Harwasch/MakeHardware/docs/00-stack.md

# The stack, and why

Every choice below was run in a real Claude Code cloud VM (Ubuntu 24.04,
4 vCPU / 16 GB / 30 GB) before it was written down. Timings are measured, not
estimated.

## What we run

| Layer | Tool | Why this one |
|---|---|---|
| Planning | **plan.yaml** + `plan-render` | Session-sized chunks with explicit dependencies, scheduled by longest path, rendered as a dependency Gantt into the README. |
| Requirements | **StrictDoc** 0.28.3 | Plain-text `.sdoc` in git, typed grammar, parent/child relations, refuses to build a tree with a dangling parent or duplicate UID. Exports HTML, JSON and ReqIF. |
| Schematic / PCB | **KiCad 10** + **[KiStack](https://github.com/American-Embedded/KiStack)** (MIT) | Ten skills, not a server: human-written house practice for schematic work, layout, BOM, exports, panelisation and Gerber review, plus a reference page for every `kicad-cli` verb. |
| PCB checks & output | **kicad-cli** | ERC, DRC, netlist, gerbers, STEP. Headless, scriptable, no GUI needed. |
| Circuit simulation | **ngspice 42** via **ltspice-mcp** 0.5.0 | Headless, no Wine, first-class backend in the MCP server. Returns parsed measurements, not plots. |
| Circuit simulation (opt-in) | **LTspice** under Wine | Only for vendor-encrypted ADI models and `.asc` editing. Off by default. |
| 3D CAD | **build123d** 0.11.1 + **build123d-mcp** | Parametric Python CAD on OCCT. Models are code, so they diff, review and re-render on a changed number. |
| Meshing / FEA | **gmsh** 4.12.1 + **CalculiX** 2.21 | Both in the Ubuntu archive, both headless. Thermal and structural. |
| Magnetics | **FastHenry** 3.0.1 + **Elmer** 26.2 (`elmerfem-csc`, elmer-csc PPA) + **GetDP** 3.2.0 | SPICE cannot tell you an inductance. FastHenry is PEEC — no air mesh, seconds for L, M, k and R_ac of air-core conductors; Elmer does the cases with ferrite in them. See the `hw-magnetics` skill for which answers what. |
| Design gates | **`sch-lint`**, **`pcb-lint`**, **`cad-export`** | In-tree, read-only, no KiCad and no MCP server needed. They measure the things ERC and DRC have no opinion about: whether a human can read the drawing, whether the net classes are physically routable, whether the CAD file is an assembly or a lump. |
| Figures | **`hw-chart`** | Eight engineering plots as themed SVG, 2-9 kB each, generated from the file that owns the numbers. |
| Design loops | **`hw-iterate`** | A ledger of every verify-and-refine pass — variables, measured metrics, the run file each number came from — and the evolution chart drawn from it. What turns "it meets the target" into something a reviewer can check. |
| Environment repair | **`hw-repair`** | Installs, at run time, what the environment build failed to — base packages, any one of phase_python's install groups, Elmer, the KiCad skill pack. A degraded snapshot is otherwise a dead session until somebody rebuilds the environment. `env/bootstrap.sh` is the from-nothing case. |
| Design review | **kicad-happy** (MIT) | Read-only analysers nothing else here has: EMC pre-compliance, thermal, voltage derating, datasheet cross-reference, distributor search. Pure Python, needs no KiCad install. |
| Vision renders | **matplotlib** + build123d tessellation | Shaded views and isometric line art from real geometry. |
| Vision styling | **Hugging Face Spaces** (FLUX Kontext, Qwen) | Restyles a geometry render without inventing new proportions. No API key needed. |

## The decisions worth arguing about

### ngspice is the default simulator, not LTspice

The original draft made LTspice authoritative. Three things argue against it:

1. `ltspice.analog.com` is **not** in the Trusted network allowlist, so the
   MSI download fails and takes the setup script down with it.
2. Wine plus the MSI is roughly 2 GB and several minutes of the ~5 minute
   environment-build budget.
3. `ltspice-mcp` treats ngspice as a first-class backend — "simulate, parse,
   diagnose, analyze… open-source path with no LTspice install".

ngspice runs headless, starts instantly and needs no allowlist change. An RC
low-pass measured `fc = 997.7 Hz` against 1 kHz theoretical on the first run.

LTspice is still worth having when you need vendor-encrypted ADI models or
`.asc` schematic editing — set `MH_ENABLE_LTSPICE=1` and add `*.analog.com`
to the allowlist. It is a supplement, not the foundation.

### KiCad 10 must come from the PPA, and that needs an allowlist entry

Ubuntu 24.04 universe carries **KiCad 7.0.11**, which has no IPC API and no
`kicad-cli` worth the name, so neither substrate works against it.
KiCad 10 is published for noble on the KiCad PPA.

The trap: PPA content is served from `ppa.launchpadcontent.net`, and the
Trusted allowlist names only `launchpad.net` and the **retired**
`ppa.launchpad.net` (which now fails to connect at all). So without a Custom
allowlist entry, `apt-get update` prints a warning, **still exits 0**, and
`apt-get install kicad` quietly installs KiCad 7 from universe. The failure is
silent and lands three steps later as "the IPC socket does not answer".

`env/setup.sh` pins the PPA with an apt preference and then explicitly asserts
the installed major version, so this fails loudly instead.

Worth knowing that the loud failure was itself wrong for a while. The check
was `apt-cache policy kicad | grep -q "kicad-10.0-releases"`, and under
`set -o pipefail` a *matching* grep exits first, `apt-cache` takes SIGPIPE, and
the pipeline reports 141. So the phase announced "PPA unreachable" on builds
where the PPA was reachable, the index fetched and the candidate correctly
pinned at 10.0.5 — and KiCad never got installed. The check now captures the
output and matches it with `case`. See `docs/01-environment.md`.

### The KiCad substrate: skills, not a tool surface

This slot has held three things. Konnect (an MCP server: one Rust binary, 214
tools over KiCad 10's IPC API) through 0.6.0; [ki-stack](https://github.com/Milind220/ki-stack)
through 0.7.0; [KiStack](https://github.com/American-Embedded/KiStack) now.
Both replacements are skills rather than servers, and that part of the argument
has held up twice:

* **A tool surface costs context whether or not it is used.** Konnect answered
  this by loading 2 of its 20 toolsets at startup and making the agent call
  `load_toolset` for the rest — which is a real cost paid in round trips and in
  failures that read as "the tool is missing". A skill costs nothing until it
  loads.
* **The failure mode is different in kind.** A missing tool is a wall. A skill
  that names its fallback is a route. That is the same reasoning `hw-optimize`
  applies to everything else in the toolbox.

`kicad-cli` has no `add`, `place`, `route` or `connect` verb on KiCad 10 and
never has, so *something* has to author. The question is only whether that is
pre-sliced verbs or the agent driving `kipy` and the design files with
judgement about which.

**Why KiStack over ki-stack.** They are different books. ki-stack is a manual
for the *substrates* — how to route between IPC, CLI and structured file edits.
KiStack is house practice from a working shop: what a good schematic looks
like, how to place before routing, when a pin swap is worth it, how to read a
Gerber. This toolbox already had the substrate question answered in
`hw-schematic` and `hw-pcb-layout`; what it did not have was the craft.

The cost is that KiStack overlaps those two skills and disagrees with them in
places — chiefly the sheet strategy, where KiStack prefers one big sheet and
this toolbox derives a sheet plan from the agreed block diagram. The rule is
**the gate wins**: `sch-lint`, `pcb-lint` and `review-gate` are what actually
fail a stage, and advice that passes review while failing a gate is not
shippable. `hw-schematic/references/kicad-channels.md` carries the table.

Neither swap kept Konnect's design-review audits or its manufacturing pipeline.
`sch-lint`, `pcb-lint`, `hw-verification` and kicad-happy cover most of that
ground, which is why the loss is acceptable — but it is a loss, not a wash.

The pack is a **pinned clone**, not a vendored copy: these are instructions an
agent follows, so an unpinned checkout means the guidance under a project can
change between sessions with nothing in the repo recording it. MIT, so
vendoring would be permitted — pinning is better because
`git -C /opt/kistack` still knows what revision it is on.

### Image generation comes from the Hugging Face connector

The vision stage wants real imagery for styling, and there is no image model in
the environment itself. The connector already attached to this account exposes
FLUX, Qwen and — the important one — `FLUX.1-Kontext-Dev`, which *edits* an
input image. Seeding it with a build123d render keeps the proportions honest
while restyling material and finish, which a pure text-to-image model cannot
do.

It needs no API key and no allowlist entry. The one catch is a `gradio=none`
header on the connector that disables `invoke`; see
`docs/01-environment.md`. A paid direct API remains the upgrade path when
shared-GPU latency stops being acceptable.

### Live IPC needs a running KiCad; nothing else does

`kicad-python` talks to an application, not a file. So board work through IPC
needs a KiCad up (`hw-kicad-up`, which starts Xvfb and the GUI), while render,
export, ERC, DRC and structured file edits all run headless.

This matters because the environment snapshot preserves **files, not
processes** — a KiCad started during setup is gone by the time a session runs.
Schematic work in particular is usually better off on the offline structured
route than on IPC, so the default posture is headless and the GUI is an
escalation.

### KiStack and kicad-happy are complementary, not competing

Both provide KiCad skills and their triggers overlap. They do different jobs:
KiStack *changes* designs, through the IPC bindings or the files themselves.
kicad-happy *reads* them — pure Python analysers producing structured reports,
plus distributor search and datasheet extraction.

So the rule is: writes go through KiStack, reads go through kicad-happy, and
the decision about which part to actually buy stays in `hw-sourcing` where the
house standards live. The full precedence table ships in the project
`CLAUDE.md`.

### The linters parse KiCad files themselves, and that is not a contradiction

The house rule — nothing writes a `.kicad_*` file except KiCad, its IPC
bindings, or a structured parser that round-trips it — stands and is not
weakened. It is about **writes**: a hand-rolled text edit corrupts those files.
Reading one is a different act, and a gate has to run headless in a container
with no KiCad and no third-party packages, so
`scripts/kicad_sexpr.py` is a ~250-line reader that does exactly that and
nothing else. Verified against both dialects present in this image: the KiCad 7
schematic fixture and KiCad 10's own shipped boards.

The board fixture the PCB linter is developed against is **generated by
`pcbnew`**, which is the escape hatch `pcb-layout.md` §0 already endorses.

### FreeCAD is not installed, and the CAD assemblies still carry their joints

STEP does not carry mates. AP242 edition 2 defines kinematics, OCCT does not
write them, and FreeCAD does not read them — so there is no portable format
that moves an editable constraint between CAD tools today.

Ubuntu 24.04 ships FreeCAD 0.21, which has no Assembly workbench at all; 1.0 is
the first version with one, and an AppImage would need an allowlist entry and
would not fit the five-minute build budget. So `cad-export` writes a **macro**
the human runs in their own FreeCAD 1.0, and runs it here only if a suitable
`freecadcmd` happens to be on `PATH`. The STEP additionally carries a named
`MATE_*` datum at every joint, which is the closest thing to a portable mate
that exists.

### This repo is a plugin, not a project

The workflow has to apply to many hardware projects that live in their own
repos, and it has to improve over time without every project being re-scaffolded.
That is what the Claude Code plugin system is for: skills, commands, agents,
hooks, MCP servers and `bin/` executables ship as one versioned unit, and a
project repo opts in with four lines in `.claude/settings.json`.

The alternative — a template repo that projects copy — was rejected because
copies diverge. A house practice learned on project three would never reach
projects one and two. With a marketplace, editing `hw-sourcing/references/`
here updates every project on the next session.

Per-project files (`plan.yaml`, `requirements/`, `docs/`) live in
`templates/project/` and are scaffolded once by `/hw-new-project`. They are
starting structure, not shared code, so divergence there is correct.

## What we rejected

| Rejected | Why |
|---|---|
| `add-apt-repository` | Depends on `apt_pkg`, which this image's Python 3.11 default cannot import. See `docs/01-environment.md`. |
| KiCad from Ubuntu universe | 7.0.11, no IPC API. |
| Konnect | Replaced in 0.7.0 — see above. It worked; the swap is about a tool surface versus a substrate the agent can drive itself. |
| Vendoring the KiCad skill pack into this repo | MIT permits it, but a pinned clone keeps upstream's authorship visible and `git -C /opt/kistack` knows its own revision. Copies go stale silently. |
| Milind220/ki-stack | A good pack, and the better one if you want the *substrate* explained. This toolbox already answers that in `hw-schematic` and `hw-pcb-layout`; it wanted the craft instead. |
| LTspice as the default | Blocked domain, ~2 GB, and unnecessary — ngspice covers the loop. |
| NGSolve, Kratos, scikit-fem | Nothing has needed them yet, and every tool in the image is one more thing that can fail the build. Add them when a project needs one. |
| Elmer from source | ~20 minutes on 1 vCPU against ~70 s for the packaged build, and it does not fit the setup budget. |
| Elmer from a prebuilt tarball on our own releases | **This is what shipped, and the asset never existed.** The pinned URL 404'd on every build in every environment; `phase_magnetics` degraded silently every time and the environment came up looking healthy with no `ElmerSolver` in it. The lesson is not "publish the asset" — it is that a private artefact nobody can verify from this repo alone is worse than a slower install. The elmer-csc PPA is upstream's own build, it is on the same host KiCad 10 already needs, and apt says loudly when it cannot fetch it. |
| `pip` for the Python stack | `uv` does the same install in **10 s** vs. minutes. |
| Doorstop, sphinx-needs | Weaker typed grammars and no ReqIF path out. |
| A template repo instead of a plugin | Copies diverge; a practice learned on one project never reaches the others. |
| A paid image API as the default | The Hugging Face connector already does it with no key and no allowlist change. Kept as a documented upgrade path. |
| Geometry renders *alone* for vision | They fix proportion but say nothing about material or finish, which is most of what a human reacts to. Geometry sets the numbers; generation does the styling. |

## Measured build budget

Setup scripts should finish in about five minutes so the filesystem snapshot
can cache. Phases run concurrently, so the wall clock is roughly the longest
one, not the sum.

| Phase | Measured |
|---|---|
| Base apt packages | 22 s |
| Python stack via uv (1.6 GB) | 10 s |
| KiStack clone + skill install | **~4 s** |
| KiCad 10 from PPA | dominated by download |
| **Total (parallel)** | **~2 min** |

LTspice, when enabled, adds roughly 2 GB and pushes this past the budget —
another reason it is opt-in.

The budget is not a soft target: overrunning it kills the script mid-phase.
That happened on a cold build where a from-source compile was still running at
the limit, and because the script's tail wrote `status.json` and the helper
commands *after* everything else, the session came up with no toolchain and no
diagnosis. The script now writes helpers first, rewrites `status.json` after
every phase, and runs its tail from an `EXIT`/`TERM` trap, so a build that is
cut short still explains itself to `hw-doctor`.
