Harwasch/MakeHardware/examples/thermal-probe/docs/review/plan.md

# Review — Project plan

`plan` · requested 2026-09-20 · branch `claude/board-docs`

Eleven chunks, nine sessions on the critical path. Layout is
blocked on the enclosure envelope, which is the dependency I am least sure
about.

## What you are agreeing to

| File | Opens in |
|---|---|
| [docs/plan.md](https://github.com/Harwasch/MakeHardware/blob/claude/board-docs/docs/plan.md) | renders on GitHub |

## For context

Sources and working files. Not part of the agreement — these change as work goes on, and changing them does not invalidate your sign-off.

**plan.svg**



| File | Opens in |
|---|---|
| [docs/plan.drawio](https://github.com/Harwasch/MakeHardware/blob/claude/board-docs/docs/plan.drawio) | draw.io / VS Code extension |
| [plan.yaml](https://github.com/Harwasch/MakeHardware/blob/claude/board-docs/plan.yaml) | plain text on GitHub |

## What we need decided

1. Is this all the work?
2. Is the order right — do you know a lead time we do not?

## Decision

**Approved** 2026-09-20 by harrison. Nothing is needed from you here.

> Add the drop test earlier if the enclosure is printed rather than
> moulded. Otherwise the order is right.

---

<sub>Generated by `review-gate`. The sign-off record is [`docs/review/reviews.yaml`](https://github.com/Harwasch/MakeHardware/blob/claude/board-docs/docs/review/reviews.yaml).</sub>
